flurl/musPICbox/pitches.c

#include <xc.h>
#include "pitches.h"

/*
 * this function sets the registers for generating a suitable
 * PWM signal for the given pitch.
 * 
 * The settings are calculated with https://www.micro-examples.com/public/microex-navig/doc/097-pwm-calculator
 * 
 * The lowest frequency a PIC16 running at 1MHZ can create  is 61Hz. So notes
 * below B1 are not implemented
 */

void setup_pitch(uint16_t pitch) {
    uint16_t duty_cycle_reg_val;
    switch(pitch) {
        case NOTE_B0:
            PR2 = 129;
            T2CON = T2CON & 0b11111100 | (3 << _T2CON_T2CKPS_POSN); // prescaler 64
            break;

        case NOTE_C1:
            PR2 = 129;
            T2CON = T2CON & 0b11111100 | (3 << _T2CON_T2CKPS_POSN); // prescaler 64
            break;

        case NOTE_CS1:
            PR2 = 129;
            T2CON = T2CON & 0b11111100 | (3 << _T2CON_T2CKPS_POSN); // prescaler 64
            break;

        case NOTE_D1:
            PR2 = 129;
            T2CON = T2CON & 0b11111100 | (3 << _T2CON_T2CKPS_POSN); // prescaler 64
            break;

        case NOTE_DS1:
            PR2 = 129;
            T2CON = T2CON & 0b11111100 | (3 << _T2CON_T2CKPS_POSN); // prescaler 64
            break;

        case NOTE_E1:
            PR2 = 97;
            T2CON = T2CON & 0b11111100 | (3 << _T2CON_T2CKPS_POSN); // prescaler 64
            break;

        case NOTE_F1:
            PR2 = 97;
            T2CON = T2CON & 0b11111100 | (3 << _T2CON_T2CKPS_POSN); // prescaler 64
            break;

        case NOTE_FS1:
            PR2 = 97;
            T2CON = T2CON & 0b11111100 | (3 << _T2CON_T2CKPS_POSN); // prescaler 64
            break;

        case NOTE_G1:
            PR2 = 97;
            T2CON = T2CON & 0b11111100 | (3 << _T2CON_T2CKPS_POSN); // prescaler 64
            break;

        case NOTE_GS1:
            PR2 = 77;
            T2CON = T2CON & 0b11111100 | (3 << _T2CON_T2CKPS_POSN); // prescaler 64
            break;

        case NOTE_A1:
            PR2 = 77;
            T2CON = T2CON & 0b11111100 | (3 << _T2CON_T2CKPS_POSN); // prescaler 64
            break;

        case NOTE_AS1:
            PR2 = 77;
            T2CON = T2CON & 0b11111100 | (3 << _T2CON_T2CKPS_POSN); // prescaler 64
            break;

        case NOTE_B1:
            PR2 = 64;
            T2CON = T2CON & 0b11111100 | (3 << _T2CON_T2CKPS_POSN); // prescaler 64
            break;

        case NOTE_C2:
            PR2 = 64;
            T2CON = T2CON & 0b11111100 | (3 << _T2CON_T2CKPS_POSN); // prescaler 64
            break;

        case NOTE_CS2:
            PR2 = 64;
            T2CON = T2CON & 0b11111100 | (3 << _T2CON_T2CKPS_POSN); // prescaler 64
            break;

        case NOTE_D2:
            PR2 = 222;
            T2CON = T2CON & 0b11111100 | (2 << _T2CON_T2CKPS_POSN); // prescaler 16
            break;

        case NOTE_DS2:
            PR2 = 222;
            T2CON = T2CON & 0b11111100 | (2 << _T2CON_T2CKPS_POSN); // prescaler 16
            break;

        case NOTE_E2:
            PR2 = 194;
            T2CON = T2CON & 0b11111100 | (2 << _T2CON_T2CKPS_POSN); // prescaler 16
            break;

        case NOTE_F2:
            PR2 = 194;
            T2CON = T2CON & 0b11111100 | (2 << _T2CON_T2CKPS_POSN); // prescaler 16
            break;

        case NOTE_FS2:
            PR2 = 173;
            T2CON = T2CON & 0b11111100 | (2 << _T2CON_T2CKPS_POSN); // prescaler 16
            break;

        case NOTE_G2:
            PR2 = 173;
            T2CON = T2CON & 0b11111100 | (2 << _T2CON_T2CKPS_POSN); // prescaler 16
            break;

        case NOTE_GS2:
            PR2 = 155;
            T2CON = T2CON & 0b11111100 | (2 << _T2CON_T2CKPS_POSN); // prescaler 16
            break;

        case NOTE_A2:
            PR2 = 141;
            T2CON = T2CON & 0b11111100 | (2 << _T2CON_T2CKPS_POSN); // prescaler 16
            break;

        case NOTE_AS2:
            PR2 = 141;
            T2CON = T2CON & 0b11111100 | (2 << _T2CON_T2CKPS_POSN); // prescaler 16
            break;

        case NOTE_B2:
            PR2 = 129;
            T2CON = T2CON & 0b11111100 | (2 << _T2CON_T2CKPS_POSN); // prescaler 16
            break;

        case NOTE_C3:
            PR2 = 119;
            T2CON = T2CON & 0b11111100 | (2 << _T2CON_T2CKPS_POSN); // prescaler 16
            break;

        case NOTE_CS3:
            PR2 = 119;
            T2CON = T2CON & 0b11111100 | (2 << _T2CON_T2CKPS_POSN); // prescaler 16
            break;

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

        case NOTE_C7:
            PR2 = 119;
            T2CON = T2CON & 0b11111100 | (0 << _T2CON_T2CKPS_POSN); // prescaler 1
            break;

        case NOTE_CS7:
            PR2 = 112;
            T2CON = T2CON & 0b11111100 | (0 << _T2CON_T2CKPS_POSN); // prescaler 1
            break;

        case NOTE_D7:
            PR2 = 106;
            T2CON = T2CON & 0b11111100 | (0 << _T2CON_T2CKPS_POSN); // prescaler 1
            break;

        case NOTE_DS7:
            PR2 = 100;
            T2CON = T2CON & 0b11111100 | (0 << _T2CON_T2CKPS_POSN); // prescaler 1
            break;

        case NOTE_E7:
            PR2 = 94;
            T2CON = T2CON & 0b11111100 | (0 << _T2CON_T2CKPS_POSN); // prescaler 1
            break;

        case NOTE_F7:
            PR2 = 89;
            T2CON = T2CON & 0b11111100 | (0 << _T2CON_T2CKPS_POSN); // prescaler 1
            break;

        case NOTE_FS7:
            PR2 = 83;
            T2CON = T2CON & 0b11111100 | (0 << _T2CON_T2CKPS_POSN); // prescaler 1
            break;

        case NOTE_G7:
            PR2 = 79;
            T2CON = T2CON & 0b11111100 | (0 << _T2CON_T2CKPS_POSN); // prescaler 1
            break;

        case NOTE_GS7:
            PR2 = 74;
            T2CON = T2CON & 0b11111100 | (0 << _T2CON_T2CKPS_POSN); // prescaler 1
            break;

        case NOTE_A7:
            PR2 = 70;
            T2CON = T2CON & 0b11111100 | (0 << _T2CON_T2CKPS_POSN); // prescaler 1
            break;

        case NOTE_AS7:
            PR2 = 66;
            T2CON = T2CON & 0b11111100 | (0 << _T2CON_T2CKPS_POSN); // prescaler 1
            break;

        case NOTE_B7:
            PR2 = 62;
            T2CON = T2CON & 0b11111100 | (0 << _T2CON_T2CKPS_POSN); // prescaler 1
            break;

        case NOTE_C8:
            PR2 = 59;
            T2CON = T2CON & 0b11111100 | (0 << _T2CON_T2CKPS_POSN); // prescaler 1
            break;

        case NOTE_CS8:
            PR2 = 55;
            T2CON = T2CON & 0b11111100 | (0 << _T2CON_T2CKPS_POSN); // prescaler 1
            break;

        case NOTE_D8:
            PR2 = 52;
            T2CON = T2CON & 0b11111100 | (0 << _T2CON_T2CKPS_POSN); // prescaler 1
            break;

        case NOTE_DS8:
            PR2 = 49;
            T2CON = T2CON & 0b11111100 | (0 << _T2CON_T2CKPS_POSN); // prescaler 1
            break;
        
        case REST:
        default:
        
    }
    
    if (pitch == REST) {
        // turn of the PWM generation
        CCP1CON &= 0b01111111;
    } else {
        // turn on the PWM generation
        CCP1CON |= 0b10000000;
    }
    
    // set the duty cycle to 50%
    // CCPRxH:CCPRxL = Ratio * 4 * (PR2+1)
    duty_cycle_reg_val = (uint16_t)(0.5*4*(PR2+1));
    CCPR1L = duty_cycle_reg_val & 255;
    CCPR1H = duty_cycle_reg_val >> 8;
    
}
